willowec/pressure-mat/board_code/src/shared/transmitter.c

/*
C file responsible for sending data over serial usb to the computer
*/

#include <stdbool.h>
#include <string.h>

#include "hardware/gpio.h"

#include "matterface.h"
#include "transmitter.h"


int parse_input(char *string)
{
    // check if the command to start reading the mat has been issued
    if (!strncmp(string, START_READING_COMMAND, sizeof(string))) {
		// start reading the mat
        return START_READING_COMMAND_ID;
	}
    else if (!strncmp(string, GET_CAL_VALS_COMMAND, sizeof(string))) {
        return GET_CAL_VALS_COMMAND_ID;
    }
    else if (!strncmp(string, PRINT_INFO_COMMAND, sizeof(string))) {
        return PRINT_INFO_COMMAND_ID;
    }
    else {
        return -1;  // no valid command read
    }
}

void initialize_transmitter()
{
    // enable UART printfs
    stdio_init_all();
}

void transmit_verification()
{
    // transmit {255, 254, 254, 255} because maximum real-world mat value is ~207
    putchar_raw(255);
    putchar_raw(254);
    putchar_raw(254);
    putchar_raw(255);
}

void transmit_row(uint8_t *row)
{
    // transmits one row over serial in hexadecimal format
    int i;
    for (i = 0; i < ROW_WIDTH; i++) {
        putchar_raw(row[i]);
    }
    fflush(stdout);

    // does not close with newline: to finish transmission, send the verification sequence
}

void transmit_mat(uint8_t *mat)
{
    sleep_ms(THROTTLE_SLEEP_MS);    // THROTTLE_SLEEP_MS set by CMake

    int i;
    for (i = 0; i < COL_HEIGHT; i++) {
        transmit_row(mat + (i * ROW_WIDTH));
    }
    transmit_verification();
}
